XavierGerD/MIDILodica/src/MIDILodica/assignNotesToButtons.ino

void assignNotesToButtons(byte startingNote, byte startingOctave, byte scale[], byte lengthOfScale) {
  byte scaleCounter = 0;
  byte currentNote = findStartingPoint(startingNote, startingOctave);

  for (byte i = 0; i < rowsLength; i++) {
    for (byte j = 0; j < columnsLength; j++) {
      noteButtons[i][j]->changeButtonNote(currentNote);
      noteButtons[i][j]->updateChannel(currentChannel);
      currentNote += scale[scaleCounter];
      scaleCounter++;
      if (scaleCounter == lengthOfScale) {
        scaleCounter = 0;
      }
    }
  }
}

void initializeButtons(byte startingNote, byte startingOctave, byte scale[], byte lengthOfScale) {
  byte scaleCounter = 0;
  byte currentNote = findStartingPoint(startingNote, startingOctave);

  for (byte i = 0; i < rowsLength; i++) {
    for (byte j = 0; j < columnsLength; j++) {
      delete noteButtons[i][j];
      noteButtons[i][j] = new NoteButton(i, j, currentNote);
      currentNote += scale[scaleCounter];
      scaleCounter++;
      if (scaleCounter == lengthOfScale) {
        scaleCounter = 0;
      }
    }
  }
}


byte findStartingPoint(byte startingNote, byte startingOctave) {
  return startingNote + 12 * startingOctave;
}
